maplac/HC-outdoor_temp/bootloader_connection.jpg

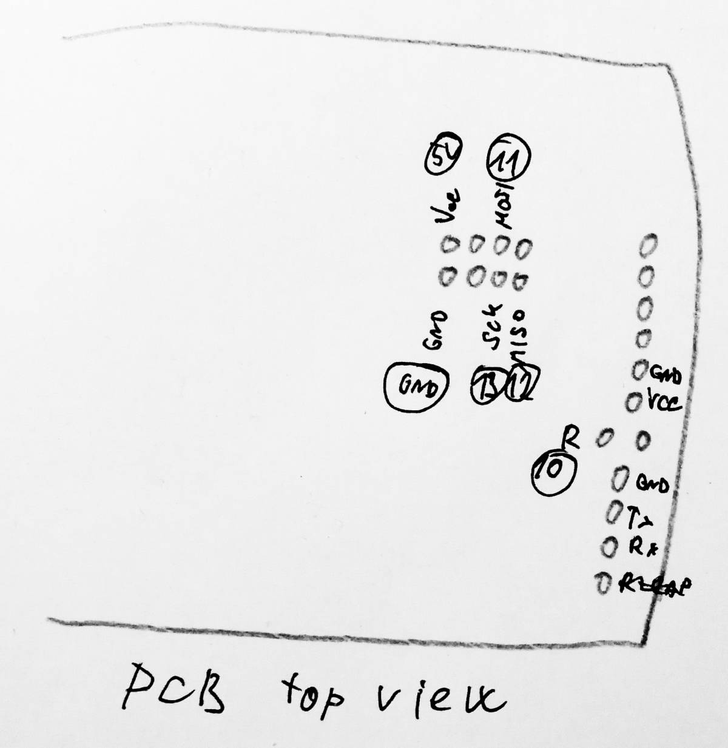
bootloader_connection.jpg
