maplac/HC-outdoor_temp/bootloader_ide_settings.jpg

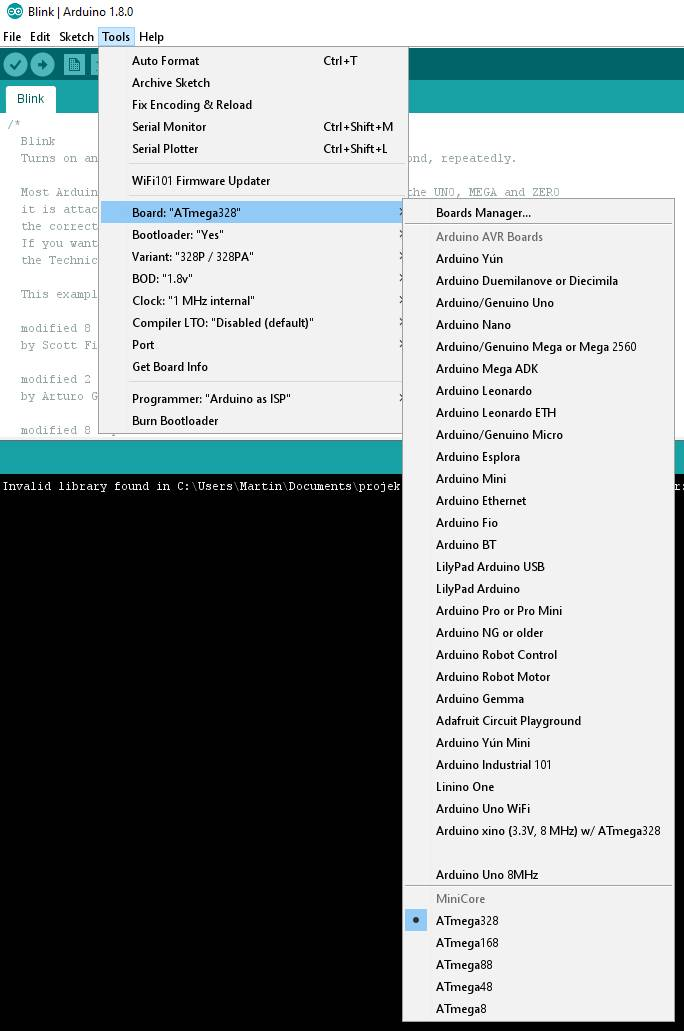
bootloader_ide_settings.jpg
